Safecast/bGeigie3/bGeigie3_endurance_august_2014/bGeigie3_placement1.jpg

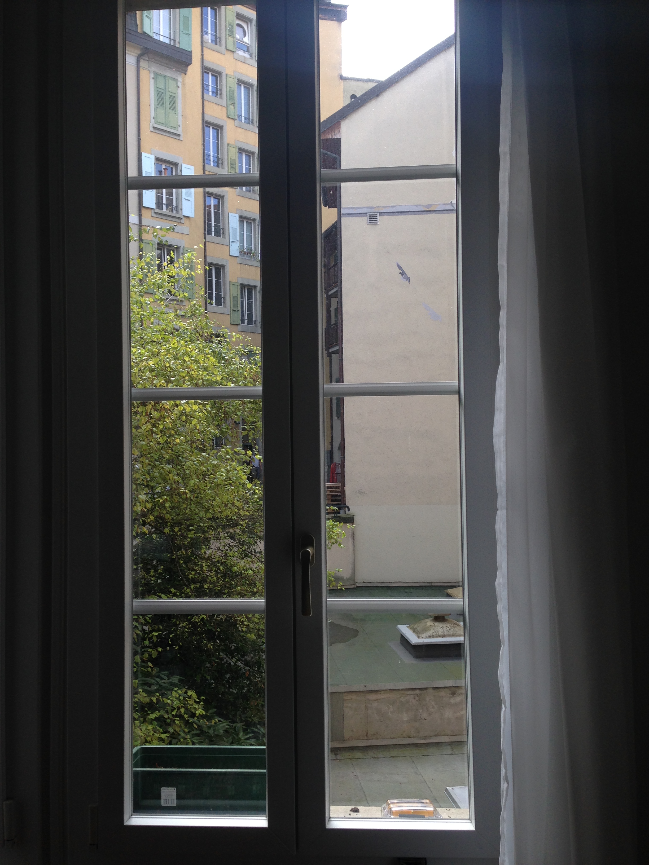
bGeigie3_endurance_august_2014/bGeigie3_placement1.jpg
